JeperoJ/Photoluminescence-scanner/Mechanical/Redesign belt/MountingPlate^Redesign belt drive - Belt^Redesign belt drive-1.STL

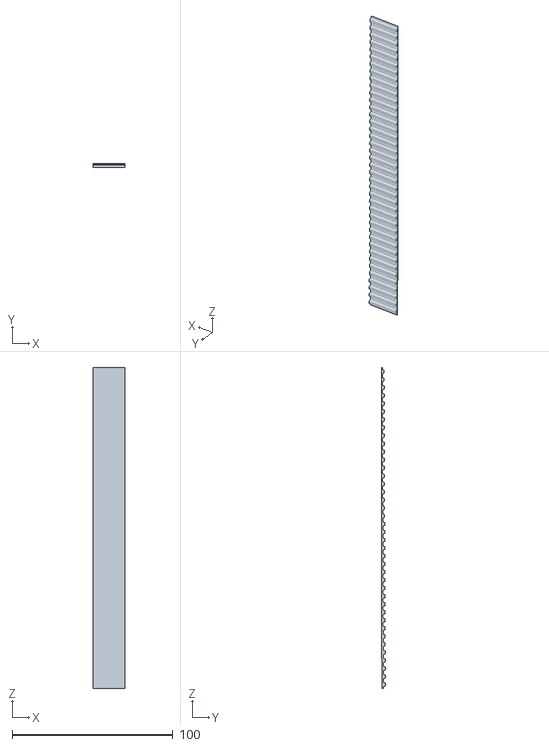
[picture p15: CAD file, 2026-01-19]
Mechanical/Redesign belt/MountingPlate^Redesign belt drive - Belt^Redesign belt drive-1.STL
20.0 x 2.34 x 200.0
