JeperoJ/Photoluminescence-scanner/Mechanical/Redesign belt/MountingPlate^Redesign belt drive - 608Bearing - Part 1.step-2.STL

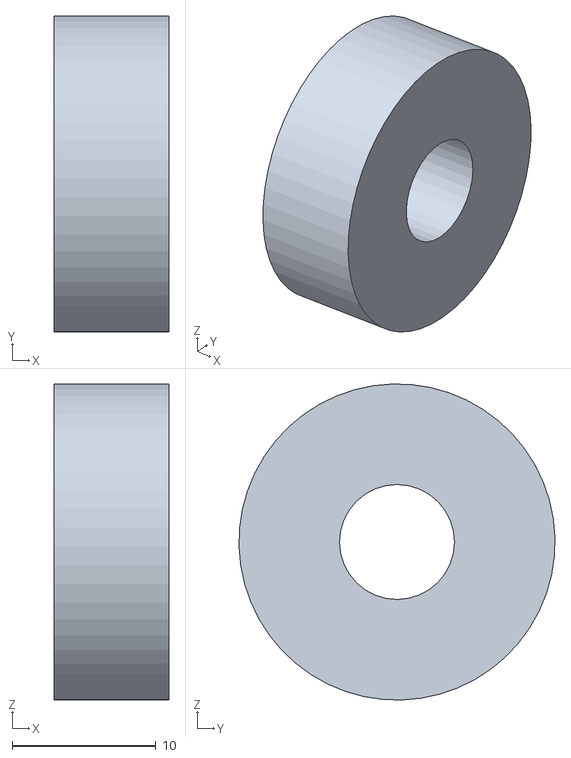
[picture p16: CAD file, 2026-01-19]
Mechanical/Redesign belt/MountingPlate^Redesign belt drive - 608Bearing - Part 1.step-2.STL
8.00 x 22.0 x 22.0
