JeperoJ/Photoluminescence-scanner/Mechanical/Redesign belt/MountingPlate^Redesign belt drive - HGW20CC1R200Z0H_ZW_FILE_1.stp-1 2026_01_08_16_23_24_0681.stp-1.STL

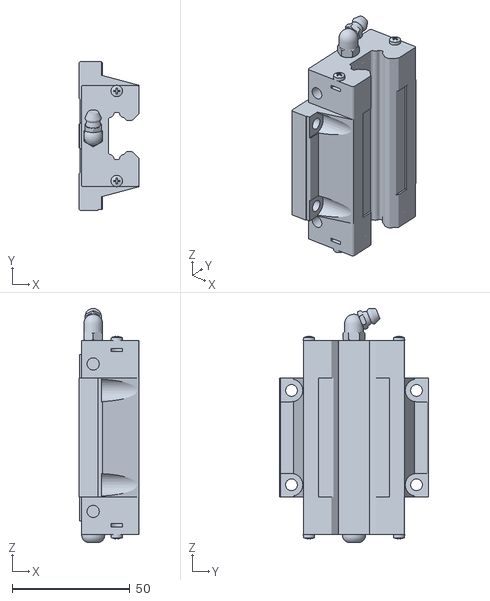
[picture p17: CAD file, 2026-01-19]
Mechanical/Redesign belt/MountingPlate^Redesign belt drive - HGW20CC1R200Z0H_ZW_FILE_1.stp-1 2026_01_08_16_23_24_0681.stp-1.STL
25.4 x 63.0 x 99.2
