JeperoJ/Photoluminescence-scanner/Mechanical/Redesign belt/MountingPlate^Redesign belt drive - NEMA23 - NEMA.step-1.STL

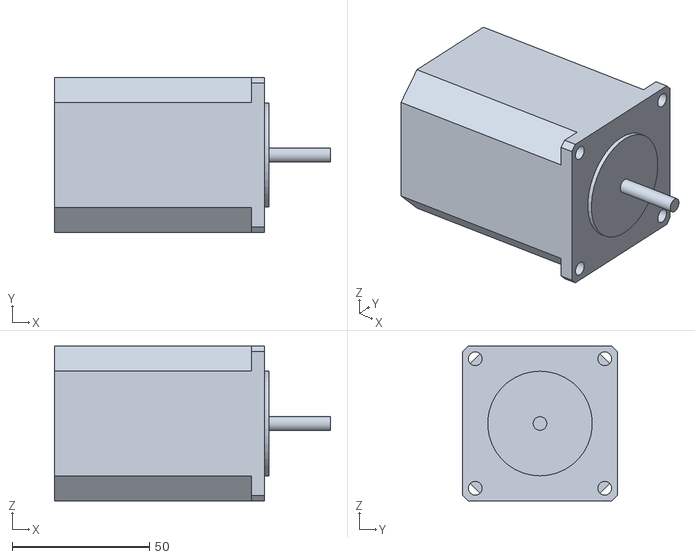
[picture p18: CAD file, 2026-01-19]
Mechanical/Redesign belt/MountingPlate^Redesign belt drive - NEMA23 - NEMA.step-1.STL
100.5 x 56.4 x 56.4
