JeperoJ/Photoluminescence-scanner/Mechanical/Redesign belt/MountingPlate^Redesign belt drive - Extrusion1^Redesign belt drive-1.STL

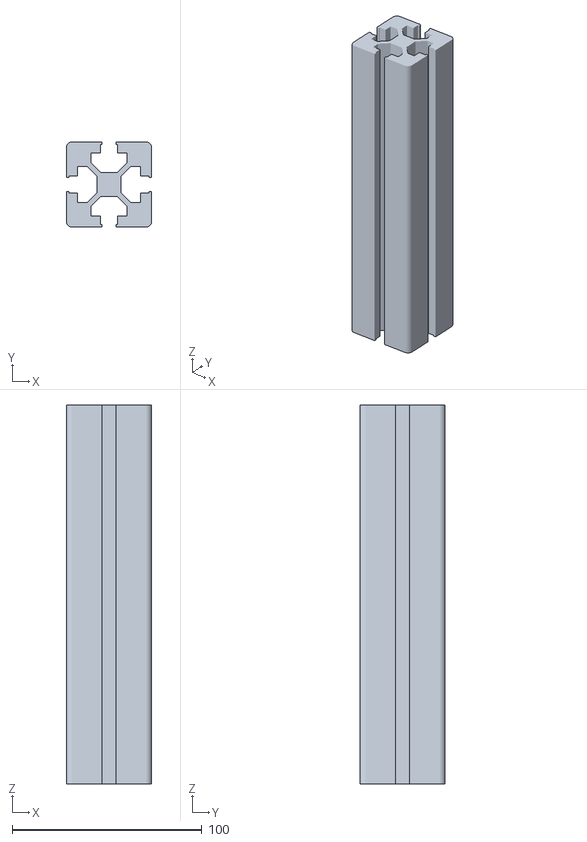
[picture p19: CAD file, 2026-01-19]
Mechanical/Redesign belt/MountingPlate^Redesign belt drive - Extrusion1^Redesign belt drive-1.STL
45.0 x 45.0 x 200.0
