JeperoJ/Photoluminescence-scanner/Mechanical/Redesign belt/MountingPlate^Redesign belt drive - MountingPlate^Redesign belt drive-1.STL

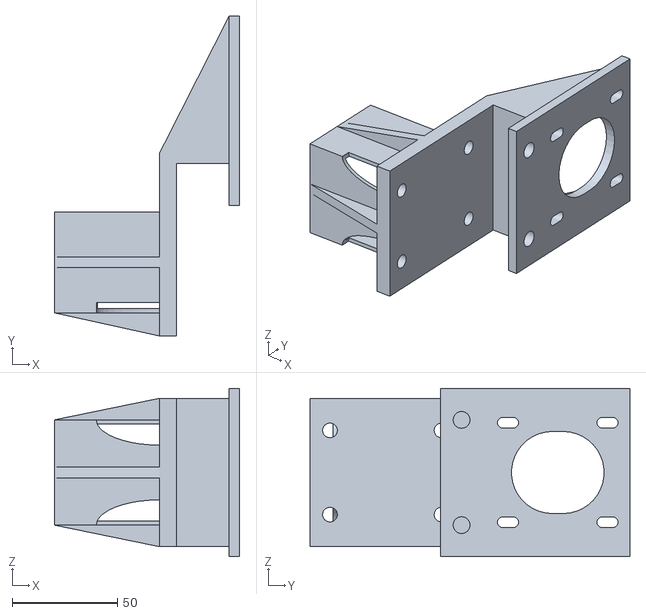
[picture p20: CAD file, 2026-01-19]
Mechanical/Redesign belt/MountingPlate^Redesign belt drive - MountingPlate^Redesign belt drive-1.STL
88.0 x 152.0 x 80.0
