JeperoJ/Photoluminescence-scanner/Mechanical/Redesign belt/27 T5 _ 14-2.stp

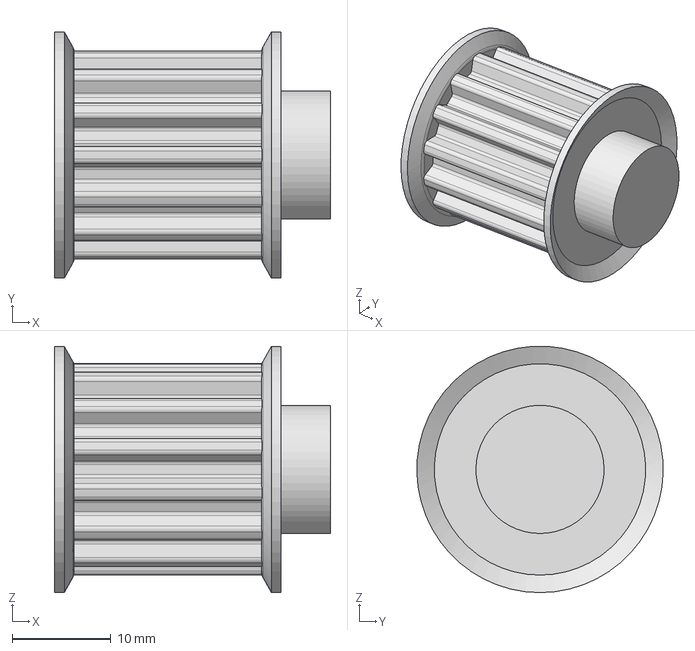
[picture p21: CAD file, 2026-01-19]
Mechanical/Redesign belt/27 T5 _ 14-2.stp
28.0 x 25.0 x 25.0 mm
