JeperoJ/Photoluminescence-scanner/Mechanical/Redesign belt/MountingPlate^Redesign belt drive - 27 T5 _ 14-2.stp-1.STL

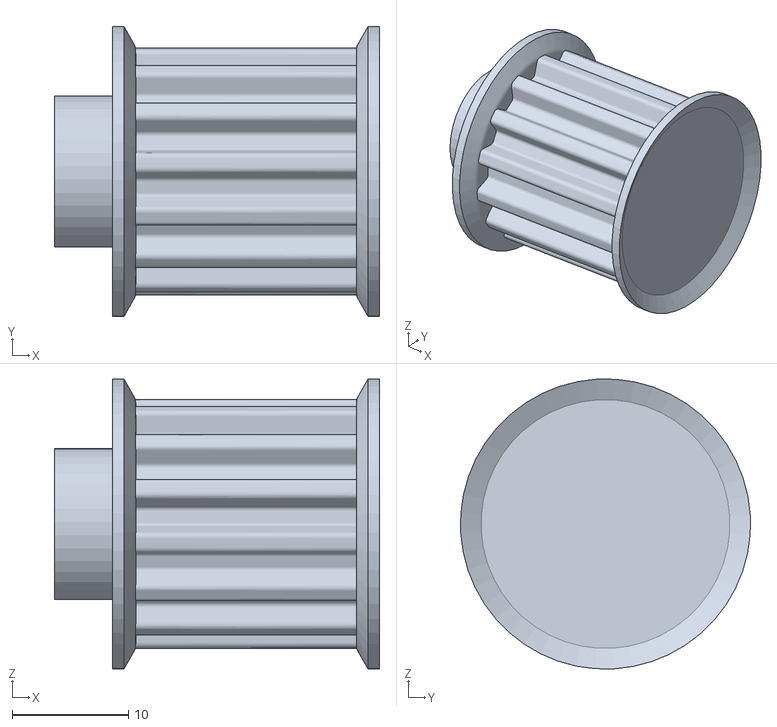
[picture p22: CAD file, 2026-01-19]
Mechanical/Redesign belt/MountingPlate^Redesign belt drive - 27 T5 _ 14-2.stp-1.STL
28.0 x 25.0 x 25.0
