JeperoJ/Photoluminescence-scanner/Mechanical/Redesign belt/HGW20CA1R78Z0C-HiwinCorporation-3D-11-12-2024.stp

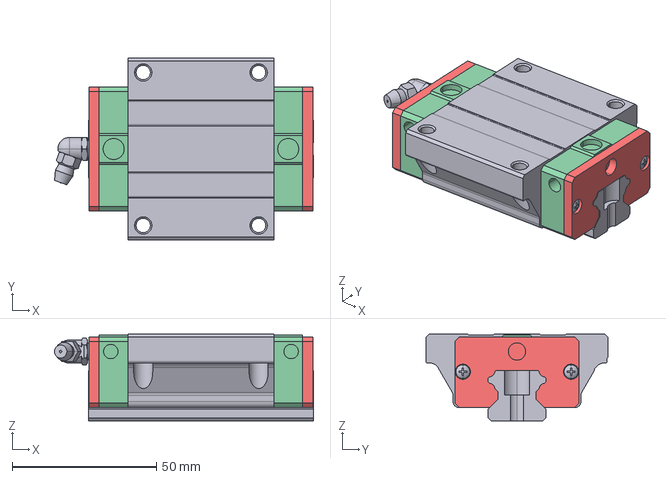
[picture p23: CAD file, 2026-01-08]
Mechanical/Redesign belt/HGW20CA1R78Z0C-HiwinCorporation-3D-11-12-2024.stp
89.8 x 63.0 x 30.0 mm
