JeperoJ/Photoluminescence-scanner/Mechanical/Redesign belt/HGW20CC1R200Z0H_ZW_FILE_1.stp

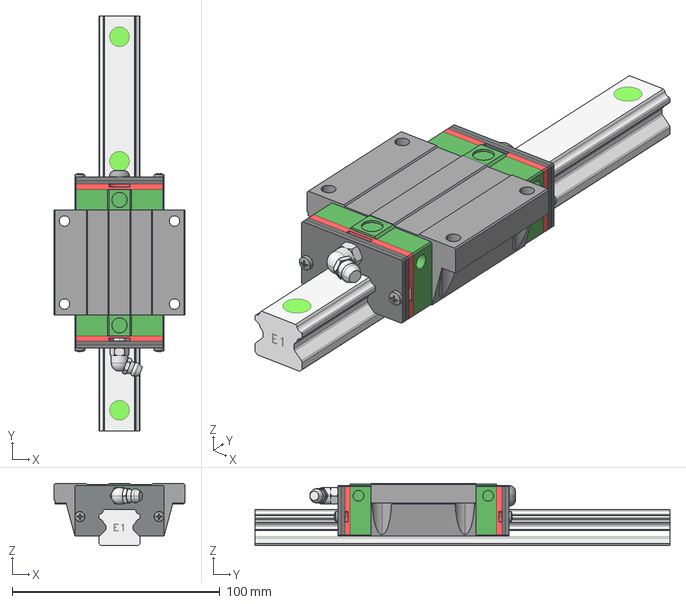
[picture p24: CAD file, 2026-01-08]
Mechanical/Redesign belt/HGW20CC1R200Z0H_ZW_FILE_1.stp
63.0 x 200.0 x 30.0 mm
