JeperoJ/Photoluminescence-scanner/Mechanical/Redesign belt/PSUMount.SLDASM

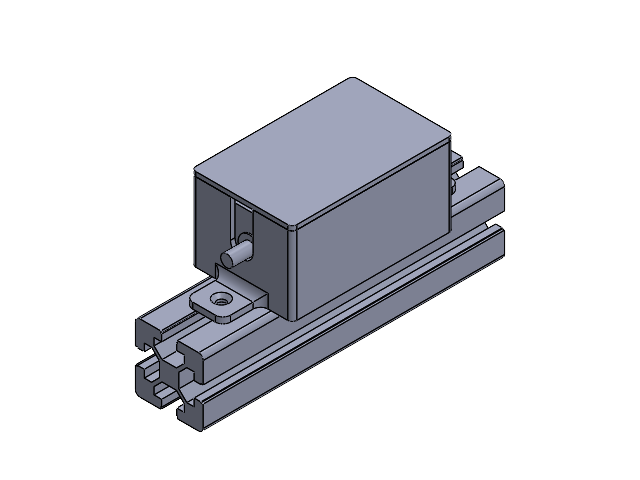
[picture p26: CAD file, 2026-03-12]
Mechanical/Redesign belt/PSUMount.SLDASM
Extrusion1^Redesign belt drive
Part2^PSUMount
Part3^PSUMount
PSUMount^PSUMount
