JeperoJ/Photoluminescence-scanner/Software refactor/LIPI_Scanning/main_v2.py

import flet as ft


def main(page: ft.Page):
    page.title = "Calc App"
    result = ft.Text(value="0")

    page.add(
        ft.Row(controls=[result]),
        ft.Row(
            controls=[
                ft.Button("AC"),
                ft.Button("+/-"),
                ft.Button("%"),
                ft.Button("/"),
            ]
        ),
        ft.Row(
            controls=[
                ft.Button("7"),
                ft.Button("8"),
                ft.Button("9"),
                ft.Button("*"),
            ]
        ),
        ft.Row(
            controls=[
                ft.Button("4"),
                ft.Button("5"),
                ft.Button("6"),
                ft.Button("-"),
            ]
        ),
        ft.Row(
            controls=[
                ft.Button("1"),
                ft.Button("2"),
                ft.Button("3"),
                ft.Button("+"),
            ]
        ),
        ft.Row(
            controls=[
                ft.Button("0", expand=2),
                ft.Button(".", expand=1),
                ft.Button("="),
            ], expand=1
        ),
    )


if __name__ == "__main__":
    ft.run(main)
